L71/0x01_max261/lookuptable.h

uint8_t divider[256] PROGMEM = {
 0x34 ,  0x32 ,  0x30 ,  0x30 ,  0x2f ,  0x2d ,  0x2c ,  0x2b ,  0x2a ,  0x2a ,  0x29 ,  0x28 , 
 0x27 ,  0x26 ,  0x25 ,  0x24 ,  0x22 ,  0x21 ,  0x21 ,  0x20 ,  0xff ,  0xfa ,  0xf0 ,  0xeb , 
 0xe7 ,  0xdf ,  0xdb ,  0xd3 ,  0xd0 ,  0xc9 ,  0xc6 ,  0xc0 ,  0xbd ,  0xb7 ,  0xb2 ,  0xb0 , 
 0xab ,  0xa6 ,  0xa2 ,  0x9e ,  0x9a ,  0x96 ,  0x93 ,  0x8f ,  0x8c ,  0x89 ,  0x84 ,  0x82 , 
 0x7f ,  0x7b ,  0x79 ,  0x75 ,  0x72 ,  0x70 ,  0x6d ,  0x6a ,  0x68 ,  0x65 ,  0x63 ,  0x60 , 
 0x5e ,  0x5b ,  0x59 ,  0x57 ,  0x55 ,  0x53 ,  0x51 ,  0x4f ,  0x4d ,  0x4b ,  0x49 ,  0x47 , 
 0x46 ,  0x44 ,  0x42 ,  0x41 ,  0x3f ,  0x3d ,  0x3c ,  0x3a ,  0x39 ,  0x38 ,  0x36 ,  0x35 , 
 0x34 ,  0x32 ,  0x31 ,  0x30 ,  0x2f ,  0x2d ,  0x2c ,  0x2b ,  0x2a ,  0x29 ,  0x28 ,  0x27 , 
 0x26 ,  0x25 ,  0x24 ,  0x23 ,  0x23 ,  0x22 ,  0x21 ,  0x20 ,  0xfd ,  0xf7 ,  0xf1 ,  0xeb , 
 0xe5 ,  0xe0 ,  0xda ,  0xd5 ,  0xd0 ,  0xcb ,  0xc6 ,  0xc1 ,  0xbc ,  0xb8 ,  0xb3 ,  0xaf , 
 0xaa ,  0xa6 ,  0xa2 ,  0x9e ,  0x9a ,  0x97 ,  0x93 ,  0x8f ,  0x8c ,  0x88 ,  0x85 ,  0x82 , 
 0x7e ,  0x7b ,  0x78 ,  0x75 ,  0x73 ,  0x70 ,  0x6d ,  0x6a ,  0x68 ,  0x65 ,  0x63 ,  0x60 , 
 0x5e ,  0x5c ,  0x59 ,  0x57 ,  0x55 ,  0x53 ,  0x51 ,  0x4f ,  0x4d ,  0x4b ,  0x49 ,  0x47 , 
 0x46 ,  0x44 ,  0x42 ,  0x41 ,  0x3f ,  0x3d ,  0x3c ,  0x3a ,  0x39 ,  0x38 ,  0x36 ,  0x35 , 
 0x34 ,  0x32 ,  0x31 ,  0x30 ,  0x2f ,  0x2e ,  0x2c ,  0x2b ,  0x2a ,  0x29 ,  0x28 ,  0x27 , 
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
  0x1 ,   0x1 ,   0x1 ,   0x1 ,   0x1 ,   0x1 ,   0x1 ,   0x1 ,   0x1 ,   0x1 ,   0x1 ,   0x1 , 
  0x1 ,   0x1 ,   0x1 ,   0x1 ,   0x1 ,   0x1 ,   0x1 ,   0x1 ,   0x1 ,   0x1 ,   0x1 ,   0x1 , 
  0x1 ,   0x1 ,   0x1 ,   0x1 };
